xanxys/scaffold/worker/src/action.hpp

#pragma once

#include <I2C.h>
#include <proto/builder.pb.h>

#include "shared_state.h"

// Safely calculate va + (vb - va) * (ix / num)
uint8_t interp(uint8_t va, uint8_t vb, uint8_t ix, uint8_t num) {
  uint8_t delta = (vb > va) ? vb - va : va - vb;
  uint8_t dv = (static_cast<uint16_t>(delta) * ix) / num;
  return (vb > va) ? va + dv : va - dv;
}

class Action {
 public:
  // Set train=0 when sensor reading > this value.
  // 255 means disable this functionality.
  uint8_t train_cutoff_thresh = 255;

  // Note this can be 0, but action still has effect.
  uint16_t duration_step;

  const static uint8_t SERVO_POS_KEEP = 0xff;
  // 20~100
  uint8_t servo_pos[N_SERVOS];

  // -0x7f~0x7f (max CCW~max CW), 0x80: keep
  const static int8_t MOTOR_VEL_KEEP = 0x80;
  int8_t motor_vel[N_MOTORS];

  Action() : Action(0) {}

  Action(uint16_t duration_ms) : duration_step(duration_ms) {
    for (int i = 0; i < N_SERVOS; i++) {
      servo_pos[i] = SERVO_POS_KEEP;
    }
    for (int i = 0; i < N_MOTORS; i++) {
      motor_vel[i] = MOTOR_VEL_KEEP;
    }
  }
};

// ActionExecState = Zero | Executing
class ActionExecState {
 private:
  // Nullable current action being executed.
  const Action* action;
  // elapsed time since starting exec of current action.
  // Don't care when action is null.
  uint16_t elapsed_step;

  uint8_t servo_pos_pre[N_SERVOS];

 public:
  ActionExecState() : action(NULL) {}

  ActionExecState(const Action* action, const uint8_t* servo_pos)
      : action(action), elapsed_step(0) {
    for (int i = 0; i < N_SERVOS; i++) {
      servo_pos_pre[i] = servo_pos[i];
    }
  }

  void step(const MultiplexedSensor& sensor, uint8_t* servo_pos_out,
            int8_t* motor_vel_out) {
    if (action == NULL) {
      return;
    }

    for (int8_t i = 0; i < N_SERVOS; i++) {
      const uint8_t targ_pos = action->servo_pos[i];
      if (targ_pos != Action::SERVO_POS_KEEP) {
        servo_pos_out[i] =
            interp(servo_pos_pre[i], targ_pos, (elapsed_step >> 5) + 1,
                   (action->duration_step >> 5) + 1);
      }
    }
    for (int8_t i = 0; i < N_MOTORS; i++) {
      const int8_t targ_vel = action->motor_vel[i];
      if (targ_vel != Action::MOTOR_VEL_KEEP) {
        motor_vel_out[i] = targ_vel;
      }
    }
    if (sensor.get_sensor_t() > action->train_cutoff_thresh) {
      motor_vel_out[MV_TRAIN] = 0;
    }
    elapsed_step++;
  }

  bool is_running() const {
    return action != NULL && (elapsed_step <= action->duration_step);
  }

  void fill_status(ExecStatus& status) const {
    status.duration_ms = action->duration_step;
    if (is_running()) {
      status.status = ExecStatus_Status_RUNNING;
      status.elapsed_ms = elapsed_step;
    } else if (action != NULL) {
      status.status = ExecStatus_Status_DONE;
      status.elapsed_ms = status.duration_ms;
    } else {
      status.status = ExecStatus_Status_IDLE;
      status.elapsed_ms = 0;
    }
  }
};

class ActionQueue {
 public:
  const static uint8_t SIZE = 8;

 private:
  Action queue[SIZE];
  uint8_t ix = 0;
  uint8_t n = 0;

 public:
  void enqueue(const Action& astate) {
    queue[(ix + n) % SIZE] = astate;
    n += 1;
  }

  Action* peek() {
    if (n == 0) {
      return NULL;
    } else {
      return &queue[ix];
    }
  }

  Action* pop() {
    if (n == 0) {
      return NULL;
    } else {
      Action* ptr = &queue[ix];
      ix = (ix + 1) % SIZE;
      n -= 1;
      return ptr;
    }
  }

  void clear() { n = 0; }

  uint8_t count() const { return n; }

  void fill_status(QueueStatus& status) const {
    status.queued = n;
    status.free = SIZE - n;
  }
};

// Must be instantiated at most only after reset.
class ActionExecutorSingleton {
 public:
  ActionQueue queue;
  ActionExecState state;

  // Position based control. Set position will be maintained automatically
  // (using Timer1) in Calibrated Servo.
  uint8_t servo_pos[N_SERVOS];

  // Velocity based control for DC motors. This class is responsible for PWM-ing
  // them, even when no action is being executed. -0x7f~0x7f (7 bit effective)
  DCMotor motors[N_MOTORS];
  int8_t motor_vel[N_MOTORS];
  int8_t motor_vel_prev[N_MOTORS];

  uint8_t gv = 0;

  static const uint8_t TCCR1A_FAST_PWM_8 = _BV(WGM10);
  static const uint8_t TCCR1B_FAST_PWM_8 = _BV(WGM12);
  static const uint8_t TCCR1A_A_NON_INVERT = _BV(COM1A1);
  static const uint8_t TCCR1A_B_NON_INVERT = _BV(COM1B1);
  static const uint8_t TCCR1B_PRESCALER_1024 = _BV(CS12) | _BV(CS10);

  static const uint8_t TCCR2A_FAST_PWM = _BV(WGM21) | _BV(WGM20);
  static const uint8_t TCCR2A_A_NON_INVERT = _BV(COM2A1);
  static const uint8_t TCCR2A_B_NON_INVERT = _BV(COM2B1);
  static const uint8_t TCCR2B_PRESCALER_1024 =
      _BV(CS22) | _BV(CS21) | _BV(CS20);

  static const uint8_t T_SEN_CACHE_SIZE = 100;
  uint8_t tr_sensor_cache[T_SEN_CACHE_SIZE];
  uint8_t tr_sensor_cache_ix;

 public:
  ActionExecutorSingleton()
      : servo_pos{50, 5},
        motors{// train
               DCMotor(0x60),
               // ori
               DCMotor(0x61),
               // screw
               DCMotor(0x62)} {}

  void init() {
    // Init servo PWM (freq_pwm=61.0Hz, dur=16.4 ms)
    TCCR2A = TCCR2A_FAST_PWM | TCCR2A_A_NON_INVERT | TCCR2A_B_NON_INVERT;
    TCCR2B = TCCR2B_PRESCALER_1024;

    // Set PWM ports as output.
    DDRB |= _BV(3);  // PWMA
    DDRD |= _BV(3);  // PWMB
    commit_posvel();
  }

  void loop1ms() {
    sensor.loop1ms();

    if (state.is_running()) {
      state.step(sensor, servo_pos, motor_vel);
      if (sensor.is_start()) {
        if (tr_sensor_cache_ix < T_SEN_CACHE_SIZE) {
          tr_sensor_cache[tr_sensor_cache_ix] = sensor.get_sensor_t();
          tr_sensor_cache_ix++;
        }
      }
      commit_posvel();
    } else {
      // Fetch new action.
      Action* new_action = queue.pop();
      state = ActionExecState(new_action, servo_pos);
      if (new_action != NULL) {
        tr_sensor_cache_ix = 0;
      }
    }
  }

  void enqueue(Action& astate) { queue.enqueue(astate); }

  bool is_idle() const { return queue.count() == 0 && !state.is_running(); }

  void fill_i2c_scan_result(I2CScanResult& result) const {
    result.type = I2CScanResult_ResultType_OK;

    const uint8_t MAX_NUM_DEVICES =
        sizeof(result.device) / sizeof(result.device[0]);
    uint8_t dev_ix = 0;
    for (uint8_t addr = 0; addr <= 0x7F; addr++) {
      DeviceCheck st = I2c.check_device(addr);
      if (st == DeviceCheck::FOUND) {
        if (dev_ix < MAX_NUM_DEVICES) {
          result.device[dev_ix++] = addr;
        } else {
          result.type = I2CScanResult_ResultType_ERROR_TOO_MANY;
          break;
        }
      } else if (st == DeviceCheck::ERR_TIMEOUT) {
        result.type = I2CScanResult_ResultType_ERROR_ABORTED;
        break;
      }
    }
    result.device_count = dev_ix;
  }

  void fill_status(Status& status) const {
    status.worker_type = WorkerType_BUILDER;
    fill_status_system(status.system);

    state.fill_status(status.exec);
    queue.fill_status(status.queue);
  }

  void fill_output_status(OutputStatus& status) const {
    // TODO: Proper index mapping
    status.loc_forward_vel = motor_vel[0];
    status.loc_rotation_vel = motor_vel[1];

    // Right block.
    status.driver_lock_vel = motor_vel[2];
    status.driver_z_pos = servo_pos[0];
    status.driver_y_pos = servo_pos[1];

    // Left block.
    status.rail_arm_pos = servo_pos[1];
  }

 private:
  void fill_status_system(SystemStatus& status) const {
    status.vcc_mv = sensor.get_vcc_mv();
    status.bat_mv = sensor.get_bat_mv();
    status.recv_byte = twelite.get_data_bytes_recv();
    status.sent_byte = twelite.get_data_bytes_sent();
    status.num_valid_packet = twelite.get_num_valid_packet();
    status.num_invalid_packet = twelite.get_num_invalid_packet();
  }

  void commit_posvel() {
    // Set PWM
    OCR2A = servo_pos[CIX_A];
    OCR2B = servo_pos[CIX_B];

    // I2C takes time, need to conserve time. Otherwise MCU become
    // unresponsive.
    for (int i = 0; i < N_MOTORS; i++) {
      if (motor_vel[i] != motor_vel_prev[i]) {
        motors[i].set_velocity(motor_vel[i]);
        motor_vel_prev[i] = motor_vel[i];
      }
    }
  }
};
