xanxys/scaffold/overmind/comm.js

import _ from 'underscore';

// Need to use window.require: https://github.com/railsware/bozon/issues/40
const SerialPort = window.require('serialport');

export default class WorkerBridge {
    constructor(handle_packet) {
        this.path = '/dev/ttyUSB0';
        this.port = new SerialPort(this.path, {
            baudRate: 115200
        }, err => {
            if (err !== null) {
                console.log('serial port error', err);
            } else {
                console.log('serial port ok');
                this.isOpen = true;
            }
        });
        this.isOpen = false;

        const parser = new SerialPort.parsers.Readline();
        this.port.pipe(parser);
        parser.on('data', data => {
            data = data.trim();

            let packet = {
                raw_data: data,
                // Decoded overmind protocol.
                src: null,
                src_ts: null,
                datagram: null,
                // Decoded datagram JSON.
                data: null,
            };

            if (data.startsWith(':7801')) {
                let ovm_packet = decode_hex(data.slice(':7801'.length, -2 /* csum */ ));

                packet.src = new DataView(ovm_packet).getUint32(0);
                packet.src_ts = new DataView(ovm_packet).getUint32(4);
                packet.datagram = new Uint8Array(ovm_packet, 8);
                try {
                    packet.data = JSON.parse(String.fromCharCode.apply(String, packet.datagram));
                } catch (e) {}
            }
            handle_packet(packet);
        });
    }

    send_command(command, addr = 0xffffffff) {
        let buffer = new ArrayBuffer(2 + 4 + command.length);
        let header = new DataView(buffer);
        header.setUint8(0, 0x78); // TWELITE addr: default child
        header.setUint8(1, 0x01); // TWELITE command: Serial
        header.setUint32(2, addr); // OVM addr
        let body = new Uint8Array(buffer, 2 + 4);
        body.set(_.map(command, ch => ch.charCodeAt(0)));

        let final_command = ':' + encode_hex(buffer) + 'X\r\n';
        console.log('send', final_command);
        this.port.write(final_command);
    }
}

function decode_hex(hex) {
    let buffer = new ArrayBuffer(hex.length / 2);
    let view = new Uint8Array(buffer);
    for (let ix = 0; ix < hex.length; ix += 2) {
        view[ix / 2] = parseInt(hex.substr(ix, 2), 16);
    }
    return buffer;
}

function encode_hex(buffer) {
    return _.map(new Uint8Array(buffer), b => (b >> 4).toString(16) + (b & 0xf).toString(16)).join('').toUpperCase();
}
